julianazim/LC-4102a_tnc/documentation/pictures/IMG_1898.JPG

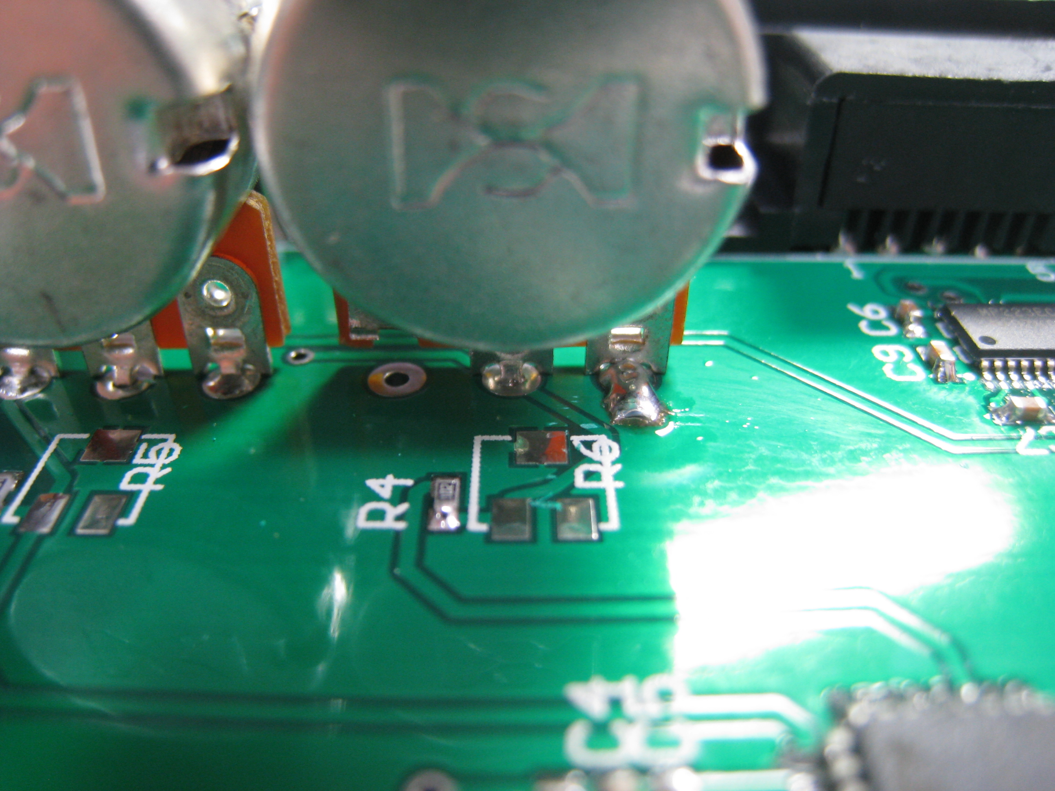
documentation/pictures/IMG_1898.JPG
