julianazim/LC-4102a_tnc/documentation/pictures/IMG_1969.JPG

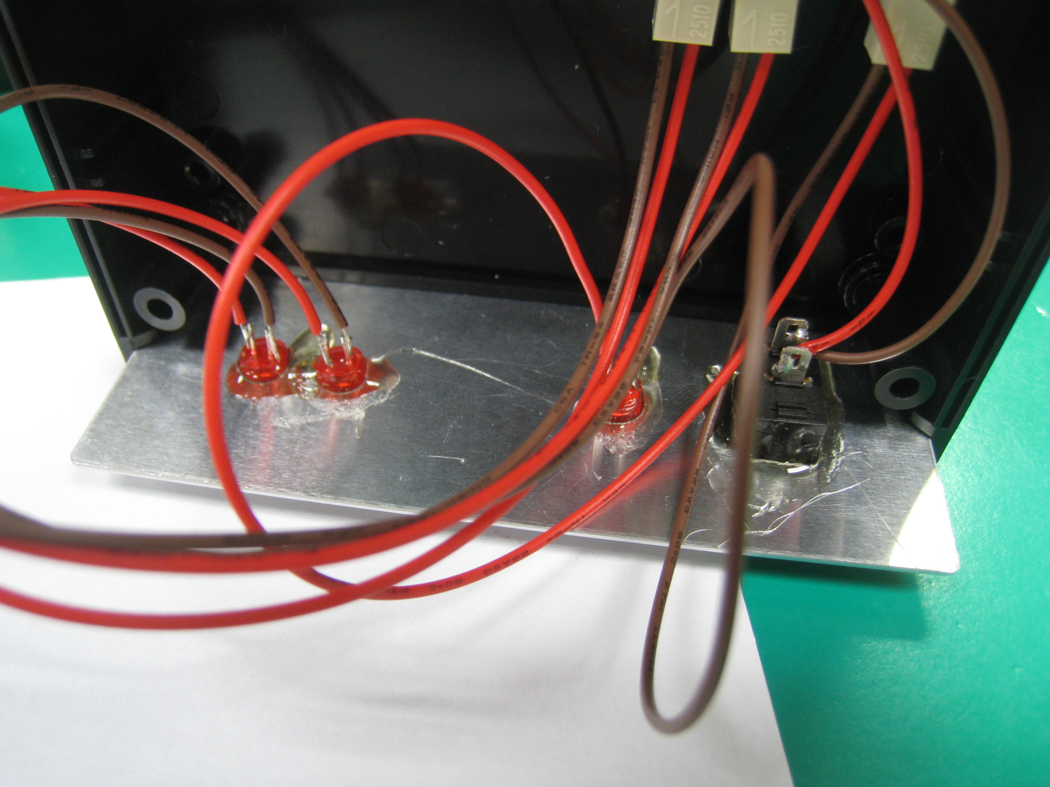
documentation/pictures/IMG_1969.JPG
