julianazim/LC-4102a_tnc/documentation/pictures/IMG_3472.JPG

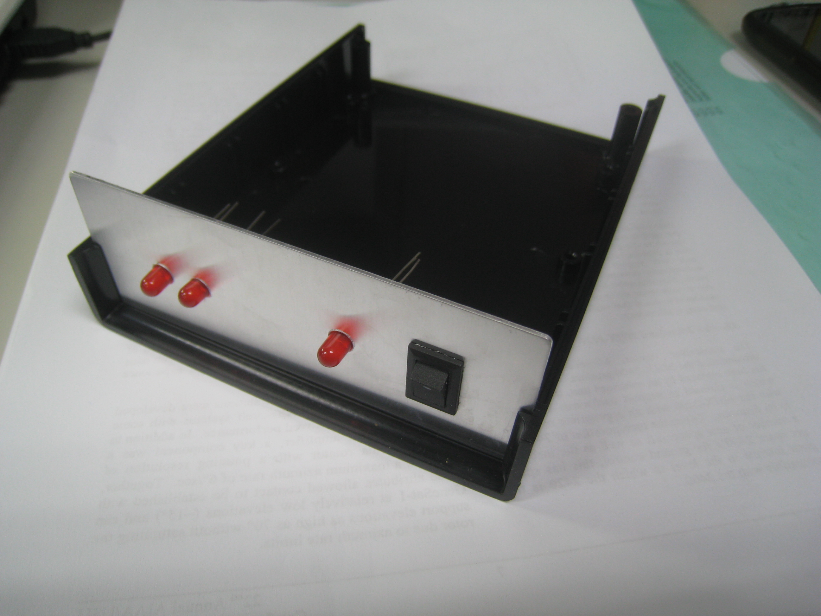
documentation/pictures/IMG_3472.JPG
