julianazim/LC-4102a_tnc/documentation/pictures/IMG_3473.JPG

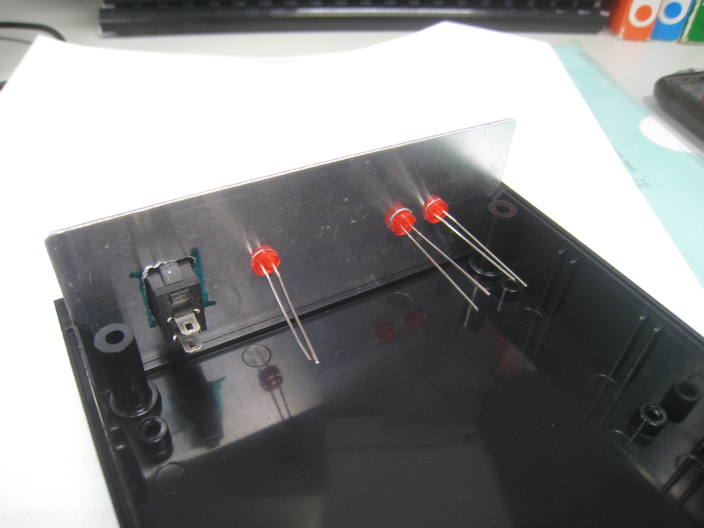
documentation/pictures/IMG_3473.JPG
