julianazim/LC-4102a_tnc/documentation/pictures/IMG_3476.JPG

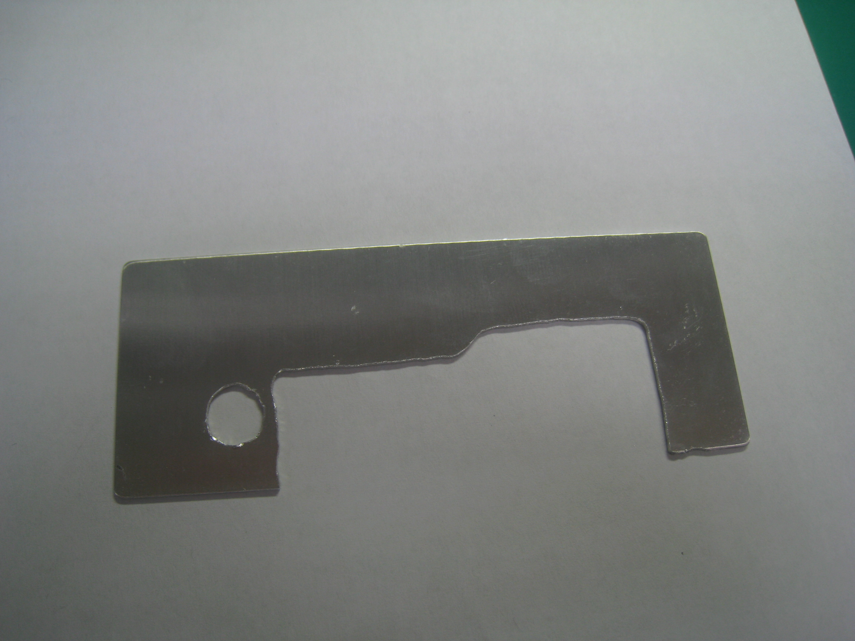
documentation/pictures/IMG_3476.JPG
