julianazim/LC-4102a_tnc/documentation/pictures/IMG_3477.JPG

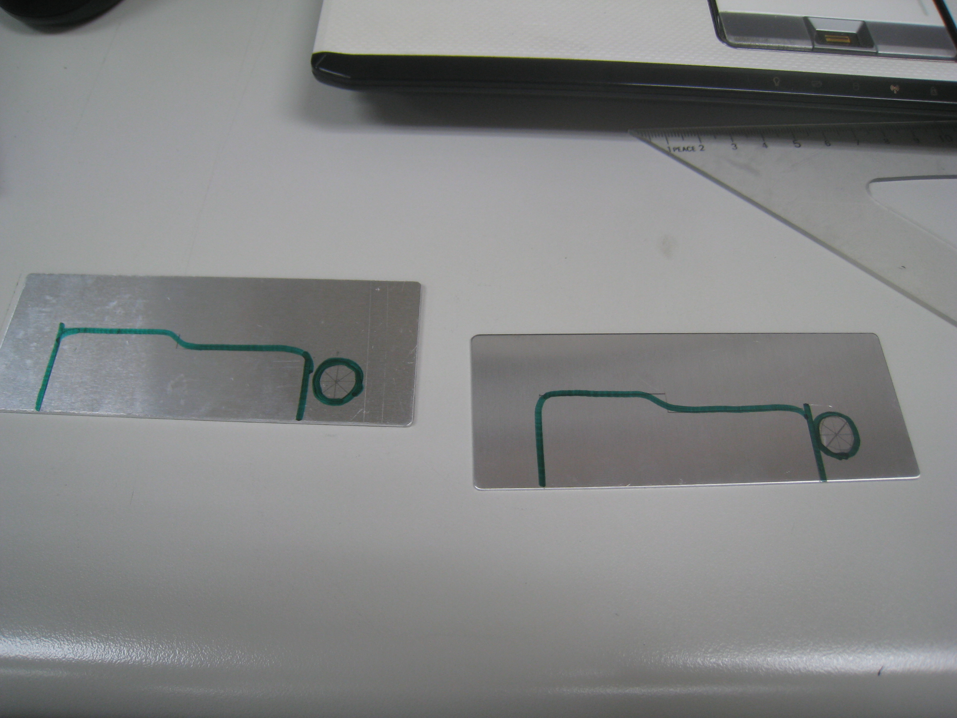
documentation/pictures/IMG_3477.JPG
